borisov-r/rfAtmega128/hardware/rev.A/rfAtmega128.sch

## KiCad design hardware/rev.A/rfAtmega128.sch (2013-09-01, an earlier design)

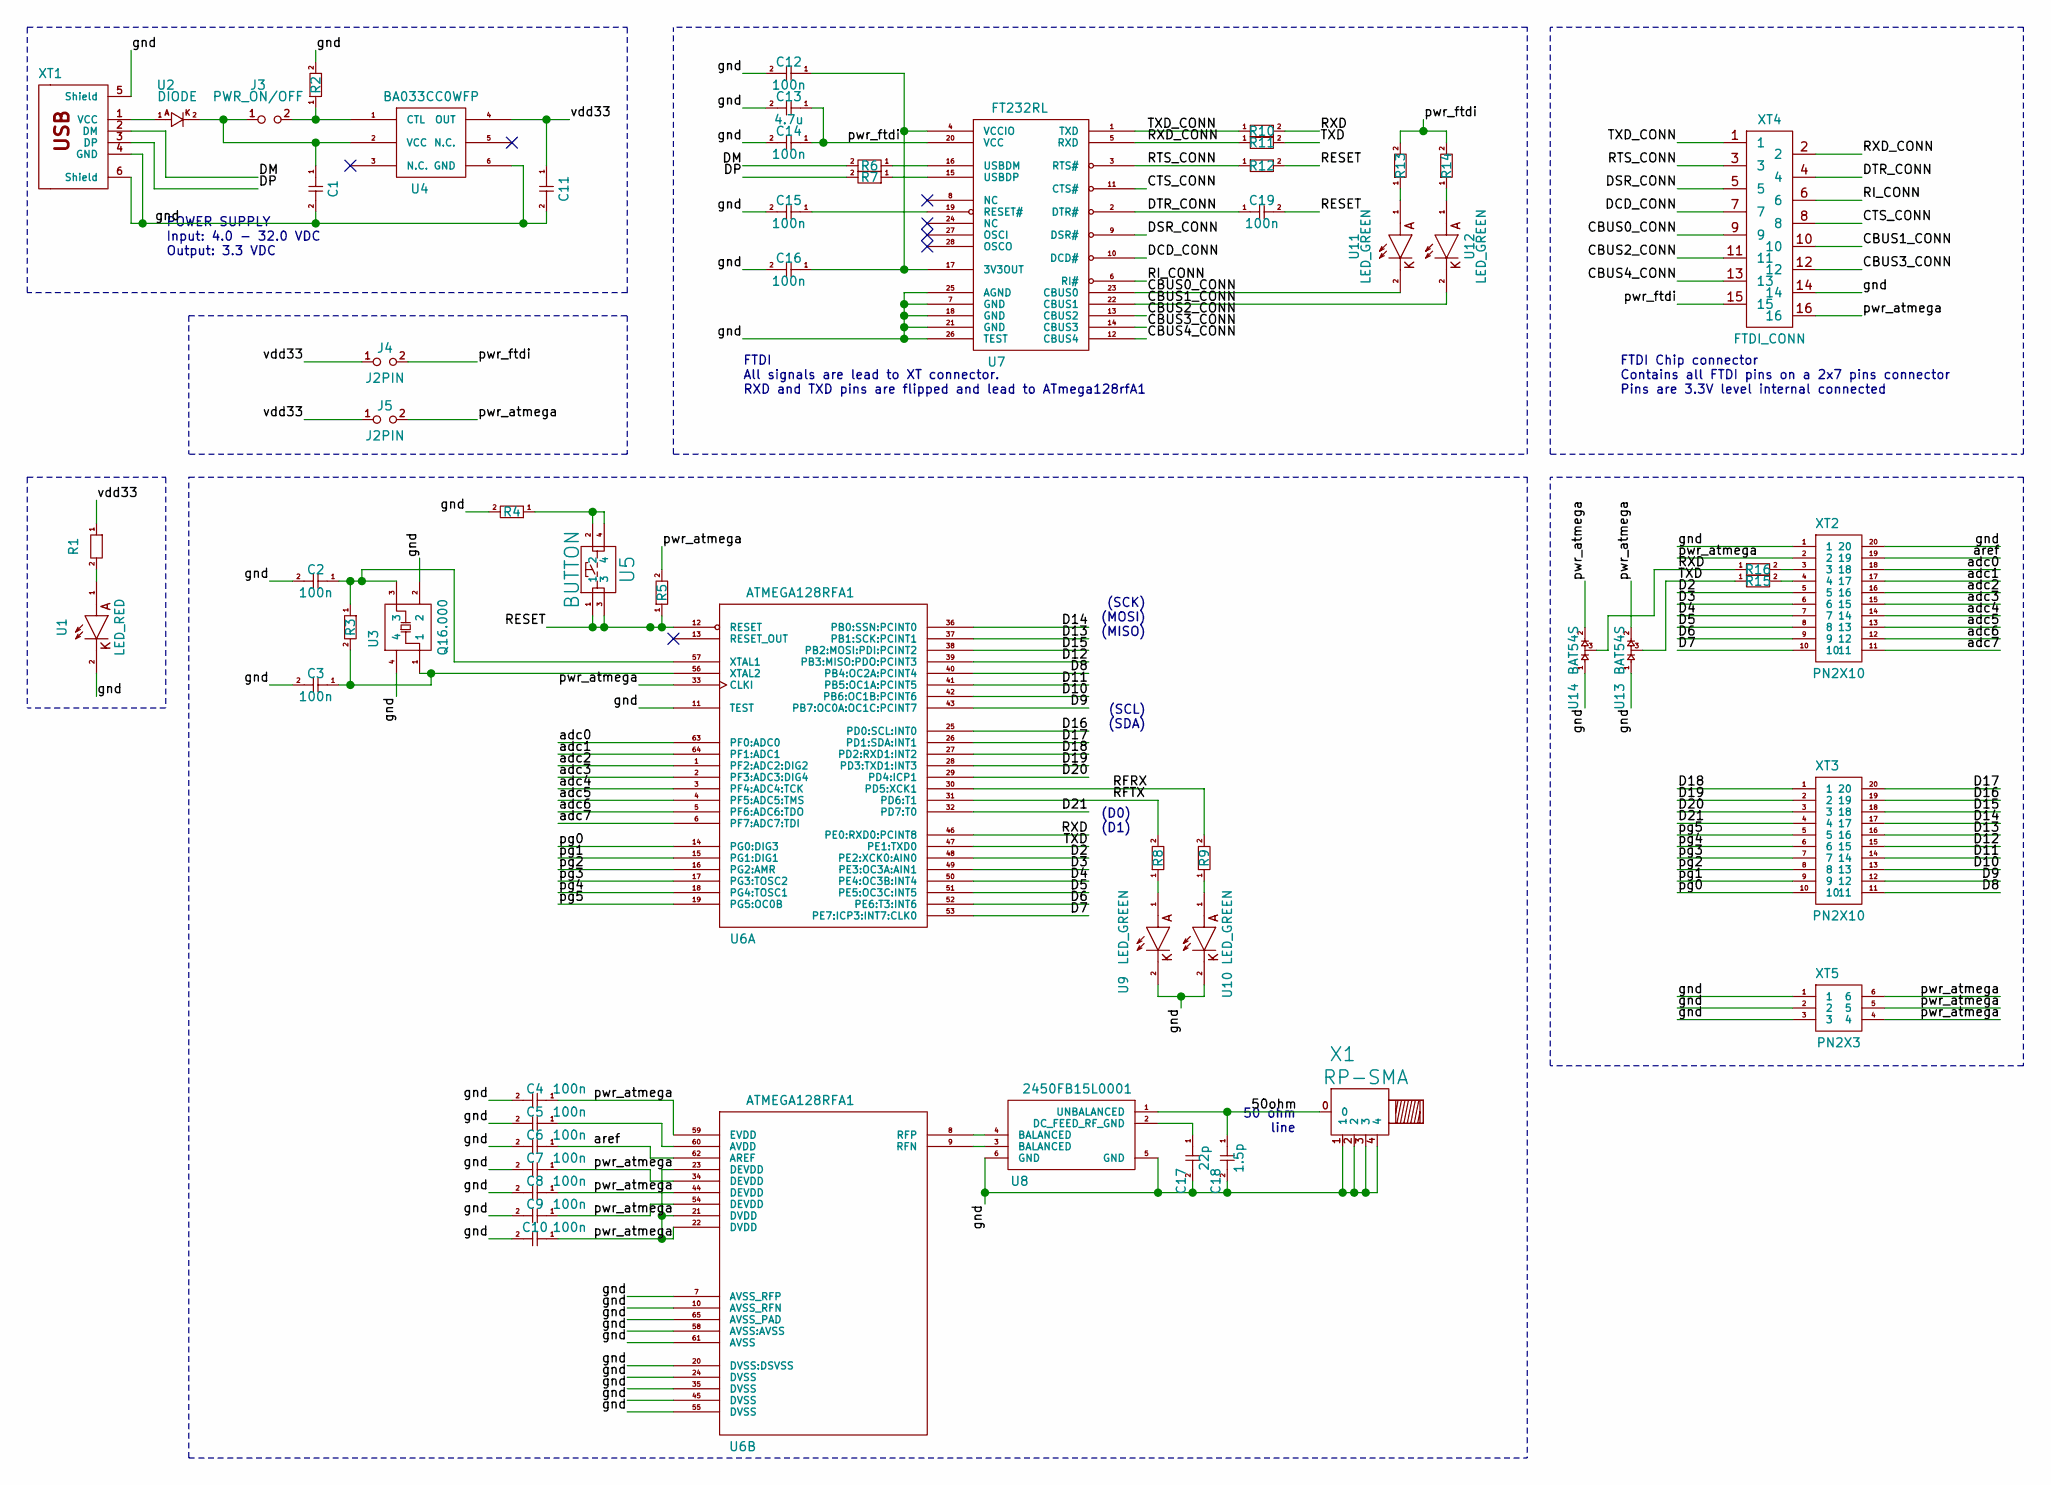
[picture p11: schematic rfAtmega128.sch]

Parts:
C1: 330n; c_0603
C2, C3, C4, C5, C6, C7, C8, C9, C10, C12, C14, C15, C16, C19: 100n; c_0603
C11: 22u; c_0805
C13: 4.7u; c_0805
C17: 22p; c_0603
C18: 1.5p; c_0603
J3: PWR_ON/OFF; JUMPER2PINS
J4, J5: J2PIN; JUMPER2PINS
R1, R13, R14: 2.7K; r_0603
R2, R8, R9, R15, R16: RES_0603; r_0603
R3: 1M; r_0603
R4: 51; r_0603
R5: 100K; r_0603
R6, R7, R10, R11, R12: 510; r_0603
U1: LED_RED; KP-2012ZGC
U2: DIODE; melf
U3: Q16.000; crystal_xg6x3p5
U4: BA033CC0WFP; BA033CCOWFP
U5: BUTTON; PCB_PUSH
U6: ATMEGA128RFA1; atmega128rfa1
U7: FT232RL; SSOP28
U8: 2450FB15L0001
U9, U10, U11, U12: LED_GREEN; KP-2012ZGC
U13, U14: BAT54S; SOT23EBC
X1: RP-SMA; rp-sma
XT1: USB_B
XT2, XT3: PN2X10
XT4: FTDI_CONN; BH16R
XT5: PN2X3

Connections:
50ohm: C18.1, U8.1 (UNBALANCED), X1.0
CBUS0_CONN: U7.23 (CBUS0), U11.2 (K), XT4.9
CBUS1_CONN: U7.22 (CBUS1), U12.2 (K), XT4.10
CBUS2_CONN: U7.13 (CBUS2), XT4.11
CBUS3_CONN: U7.14 (CBUS3), XT4.12
CBUS4_CONN: U7.12 (CBUS4), XT4.13
CTS_CONN: U7.11 (CTS#), XT4.8
D2: U6.48 (PE2:XCK0:AIN0), XT2.5
D3: U6.49 (PE3:OC3A:AIN1), XT2.6
D4: U6.50 (PE4:OC3B:INT4), XT2.7
D5: U6.51 (PE5:OC3C:INT5), XT2.8
D6: U6.52 (PE6:T3:INT6), XT2.9
D7: U6.53 (PE7:ICP3:INT7:CLK0), XT2.10
D8: U6.40 (PB4:OC2A:PCINT4), XT3.11
D9: U6.43 (PB7:OC0A:OC1C:PCINT7), XT3.12
D10: U6.42 (PB6:OC1B:PCINT6), XT3.13
D11: U6.41 (PB5:OC1A:PCINT5), XT3.14
D12: U6.39 (PB3:MISO:PDO:PCINT3), XT3.15
D13: U6.37 (PB1:SCK:PCINT1), XT3.16
D14: U6.36 (PB0:SSN:PCINT0), XT3.17
D15: U6.38 (PB2:MOSI:PDI:PCINT2), XT3.18
D16: U6.25 (PD0:SCL:INT0), XT3.19
D17: U6.26 (PD1:SDA:INT1), XT3.20
D18: U6.27 (PD2:RXD1:INT2), XT3.1
D19: U6.28 (PD3:TXD1:INT3), XT3.2
D20: U6.29 (PD4:ICP1), XT3.3
D21: U6.32 (PD7:T0), XT3.4
DCD_CONN: U7.10 (DCD#), XT4.7
DM: R6.2, XT1.2 (DM)
DP: R7.2, XT1.3 (DP)
DSR_CONN: U7.9 (DSR#), XT4.5
DTR_CONN: C19.1, U7.2 (DTR#), XT4.4
unnamed: C1.1, J3.1, U2.2 (K), U4.2 (VCC)
unnamed: C2.1, R3.1, U3.3, U6.57 (XTAL1)
unnamed: C3.1, R3.2, U3.1, U6.56 (XTAL2)
unnamed: C5.1, U6.60 (AVDD)
unnamed: C12.1, C16.1, U7.4 (VCCIO), U7.17 (3V3OUT)
unnamed: C15.1, U7.19 (RESET#)
unnamed: C17.1, U8.2 (DC_FEED_RF_GND)
unnamed: J3.2, R2.1, U4.1 (CTL)
unnamed: R1.2, U1.1 (A)
unnamed: R4.1, U5.2, U5.4
unnamed: R6.1, U7.16 (USBDM)
unnamed: R7.1, U7.15 (USBDP)
unnamed: R8.1, U9.1 (A)
unnamed: R9.1, U10.1 (A)
unnamed: R13.1, U11.1 (A)
unnamed: R14.1, U12.1 (A)
unnamed: R15.2, XT2.4
unnamed: R16.2, XT2.3
unnamed: U2.1 (A), XT1.1 (VCC)
unnamed: U6.8 (RFP), U8.4 (BALANCED)
unnamed: U6.9 (RFN), U8.3 (BALANCED)
RESET: C19.2, R5.1, R12.2, U5.1, U5.3, U6.12 (RESET)
RFRX: R9.2, U6.30 (PD5:XCK1)
RFTX: R8.2, U6.31 (PD6:T1)
RI_CONN: U7.6 (RI#), XT4.6
RTS_CONN: R12.1, U7.3 (RTS#), XT4.3
RXD: R10.2, R16.1, U6.46 (PE0:RXD0:PCINT8), U14.3
RXD_CONN: R11.1, U7.5 (RXD), XT4.2
TXD: R11.2, R15.1, U6.47 (PE1:TXD0), U13.3
TXD_CONN: R10.1, U7.1 (TXD), XT4.1
adc0: U6.63 (PF0:ADC0), XT2.18
adc1: U6.64 (PF1:ADC1), XT2.17
adc2: U6.1 (PF2:ADC2:DIG2), XT2.16
adc3: U6.2 (PF3:ADC3:DIG4), XT2.15
adc4: U6.3 (PF4:ADC4:TCK), XT2.14
adc5: U6.4 (PF5:ADC5:TMS), XT2.13
adc6: U6.5 (PF6:ADC6:TDO), XT2.12
adc7: U6.6 (PF7:ADC7:TDI), XT2.11
aref: C6.1, U6.62 (AREF), XT2.19
gnd: C1.2, C2.2, C3.2, C4.2, C5.2, C6.2, C7.2, C8.2, C9.2, C10.2, C11.2, C12.2, C13.2, C14.2, C15.2, C16.2, C17.2, C18.2, R2.2, R4.2, U1.2 (K), U3.2, U3.4, U4.6 (GND), U6.7 (AVSS_RFP), U6.10 (AVSS_RFN), U6.11 (TEST), U6.20 (DVSS:DSVSS), U6.24 (DVSS), U6.35 (DVSS), U6.45 (DVSS), U6.55 (DVSS), U6.58 (AVSS:AVSS), U6.61 (AVSS), U6.65 (AVSS_PAD), U7.7 (GND), U7.18 (GND), U7.21 (GND), U7.25 (AGND), U7.26 (TEST), U8.5 (GND), U8.6 (GND), U9.2 (K), U10.2 (K), U13.1, U14.1, X1.1, X1.2, X1.3, X1.4, XT1.4 (GND), XT1.5 (Shield), XT1.6 (Shield), XT2.1, XT2.20, XT4.14, XT5.1, XT5.2, XT5.3
pg0: U6.14 (PG0:DIG3), XT3.10
pg1: U6.15 (PG1:DIG1), XT3.9
pg2: U6.16 (PG2:AMR), XT3.8
pg3: U6.17 (PG3:TOSC2), XT3.7
pg4: U6.18 (PG4:TOSC1), XT3.6
pg5: U6.19 (PG5:OC0B), XT3.5
pwr_atmega: C4.1, C7.1, C8.1, C9.1, C10.1, J5.2, R5.2, U6.21 (DVDD), U6.22 (DVDD), U6.23 (DEVDD), U6.33 (CLKI), U6.34 (DEVDD), U6.44 (DEVDD), U6.54 (DEVDD), U6.59 (EVDD), U13.2, U14.2, XT2.2, XT4.16, XT5.4, XT5.5, XT5.6
pwr_ftdi: C13.1, C14.1, J4.2, R13.2, R14.2, U7.20 (VCC), XT4.15
vdd33: C11.1, J4.1, J5.1, R1.1, U4.4 (OUT)

Notes on the sheet:
50 ohm line
(SCK) (MOSI) (MISO)
(SCL) (SDA)
(D0) (D1)
FTDI Chip connector Contains all FTDI pins on a 2x7 pins connector Pins are 3.3V level internal connected
FTDI All signals are lead to XT connector. RXD and TXD pins are flipped and lead to ATmega128rfA1
POWER SUPPLY Input: 4.0 - 32.0 VDC Output: 3.3 VDC
