borisov-r/rfAtmega128/hardware/initialBoardWithLibraries/arduino_compatible_board/arduino_uno_r3_compatible.sch

## KiCad design hardware/initialBoardWithLibraries/arduino_compatible_board/arduino_uno_r3_compatible.sch (2012-04-18)

Schematic: arduino_uno_r3_compatible.sch

Parts:
C1: 0.1uF; SM0805
C2, C3, C13, C14: 22pF; 0805
C4: 47uF/25V; 1206
C5: 1uF; 1206
C6, C10: 0.1uF; 0805
C7: 47uF/12V; 1206
C8, C12: 0.01uF; 0805
C9: 1uF/9V; 1206
C11: 0.01Uf; 0805
D1: DIODE; DO214AA
D2: CD1206-S01575; 1206
D3: LED YELLOW; 0805
D4: LED YELLOW (TX); 0805
D5: LED YELLOW (RX); 0805
D6: LED GREEN; 0805
D7: CD1206; 1206
F1: MF-MSMF050-2 500mA
IC1: ATMEGA16U2
IC2: ATMEGA328-P
J1: USB
J2: JACK_2P
JP1: JUMPER
JP2: CONN_2X2
L1: BLM21
P1, P3: CONN_3X2
P2, P6: CONN_8
P4: CONN_10
P5: CONN_6
Q1: FDN340P
R1, R2, R6, R16: 10K; 0805
R3, R4: 22E; 0805
R5, R17: 1M; 0805
R7: 333E; 0805
R8, R10, R11, R12, R13, R14, R15: 1K; 0805
R9: 220E; 0805
SW1: SW_PUSH
U1: LM358
U2: 7805
U3: LM317_SOT223
VR1, VR2: CG0603MLC-05E
X1, X2: 16MHz

Notes on the sheet:
License : CC BY-SA http://creativecommons.org/licenses/by-sa/3.0/ Based on Arduino Uno R3 design from http://arduino.cc
POWER
ICSP
