borisov-r/rfAtmega128/firmware/arduino-1.0.3/hardware/arduino/cores/rfAtmega128/main.cpp

#define ARDUINO_MAIN
#include <Arduino.h>

int main(void)
{
	init();

#if defined(USBCON)
	USB.attach();
#endif
	
	setup();
    
	for (;;) {
		loop();
		if (serialEventRun) serialEventRun();
	}
        
	return 0;
}
